sondresjolyst/liz-sensors/src/helpers/WIZHelper.h

// Copyright (c) 2023-2025 Sondre Sjølyst

#ifndef SRC_HELPERS_WIZHELPER_H_
#define SRC_HELPERS_WIZHELPER_H_

#include <ArduinoJson.h>
#include <WiFiUdp.h>

constexpr unsigned int localUdpPort = 38899;
extern WiFiUDP Udp;

void wizSetup();

#endif  // SRC_HELPERS_WIZHELPER_H_
